nskemish/medmentum/application/fltr/png/ADDBTN.png

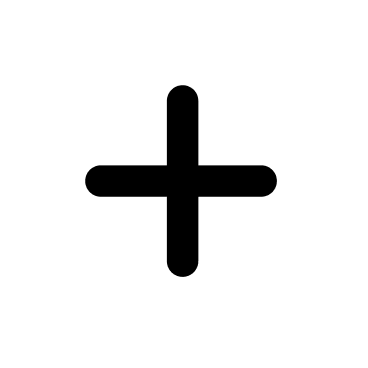
application/fltr/png/ADDBTN.png
