nskemish/medmentum/application/fltr/png/BATTERY.png

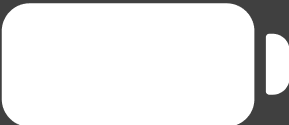
application/fltr/png/BATTERY.png
