nskemish/medmentum/application/fltr/png/DELBTN.png

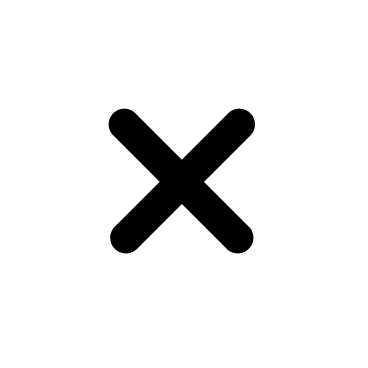
application/fltr/png/DELBTN.png
