nskemish/medmentum/application/fltr/png/DOZERI_IKONA.png

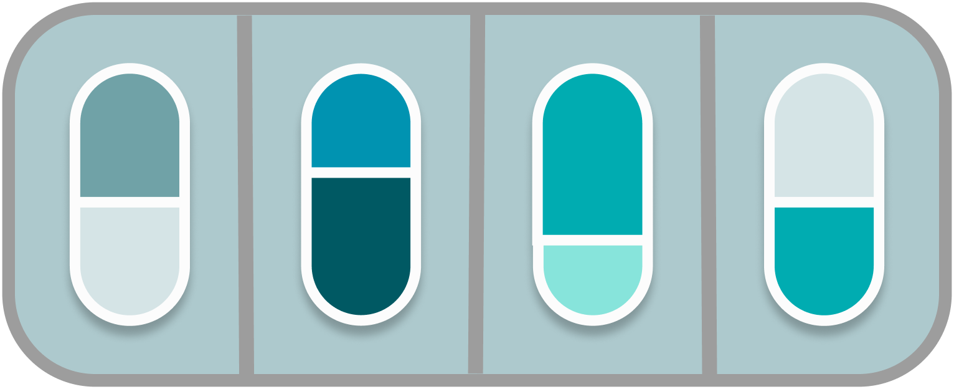
application/fltr/png/DOZERI_IKONA.png
