nskemish/medmentum/application/fltr/png/Ellipse 1.png

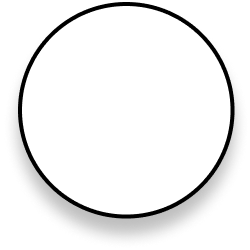
application/fltr/png/Ellipse 1.png
