nskemish/medmentum/application/fltr/png/Ellipse 2.png

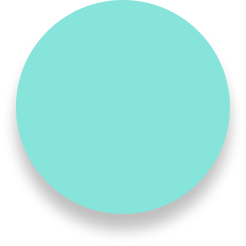
application/fltr/png/Ellipse 2.png
