nskemish/medmentum/application/fltr/png/OTKACENO.png

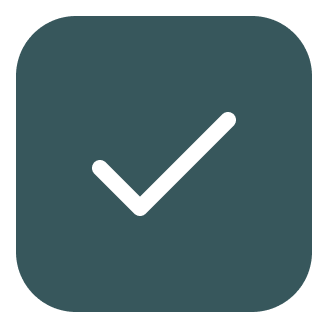
application/fltr/png/OTKACENO.png
