nskemish/medmentum/application/fltr/png/PILULA.png

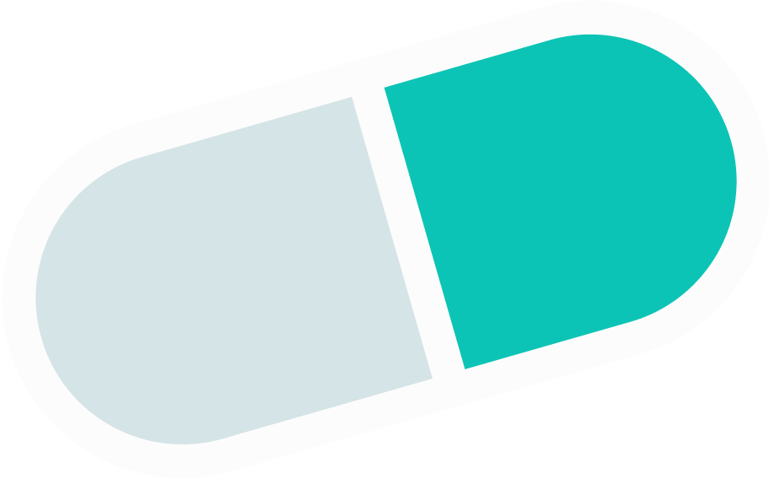
application/fltr/png/PILULA.png
