nskemish/medmentum/application/fltr/png/POVEZIVANJEDUGME.png

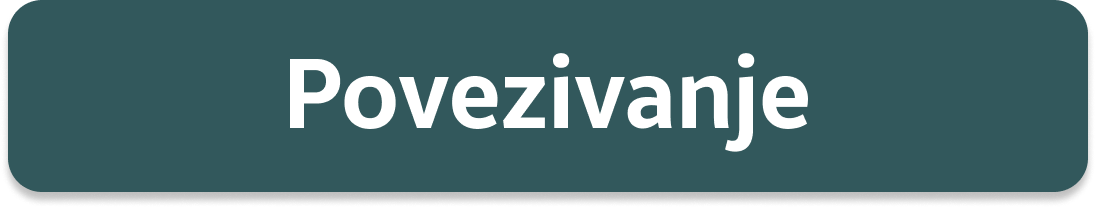
application/fltr/png/POVEZIVANJEDUGME.png
