nskemish/medmentum/device/hw/$d/slk/bulb-svgrepo-com.png

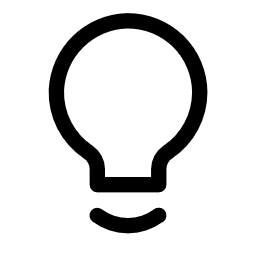
device/hw/$d/slk/bulb-svgrepo-com.png
