nskemish/medmentum/device/hw/$d/slk/MedMentum.png

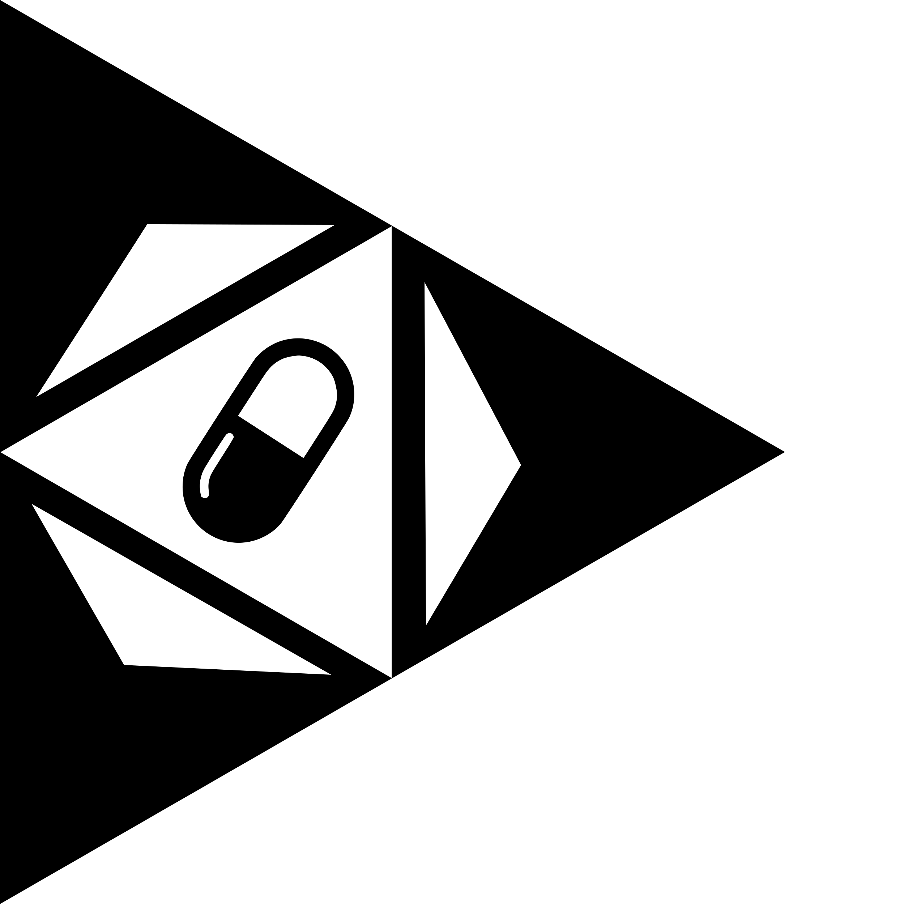
device/hw/$d/slk/MedMentum.png
