nskemish/medmentum/device/hw/$d/slk/NoviSad.png

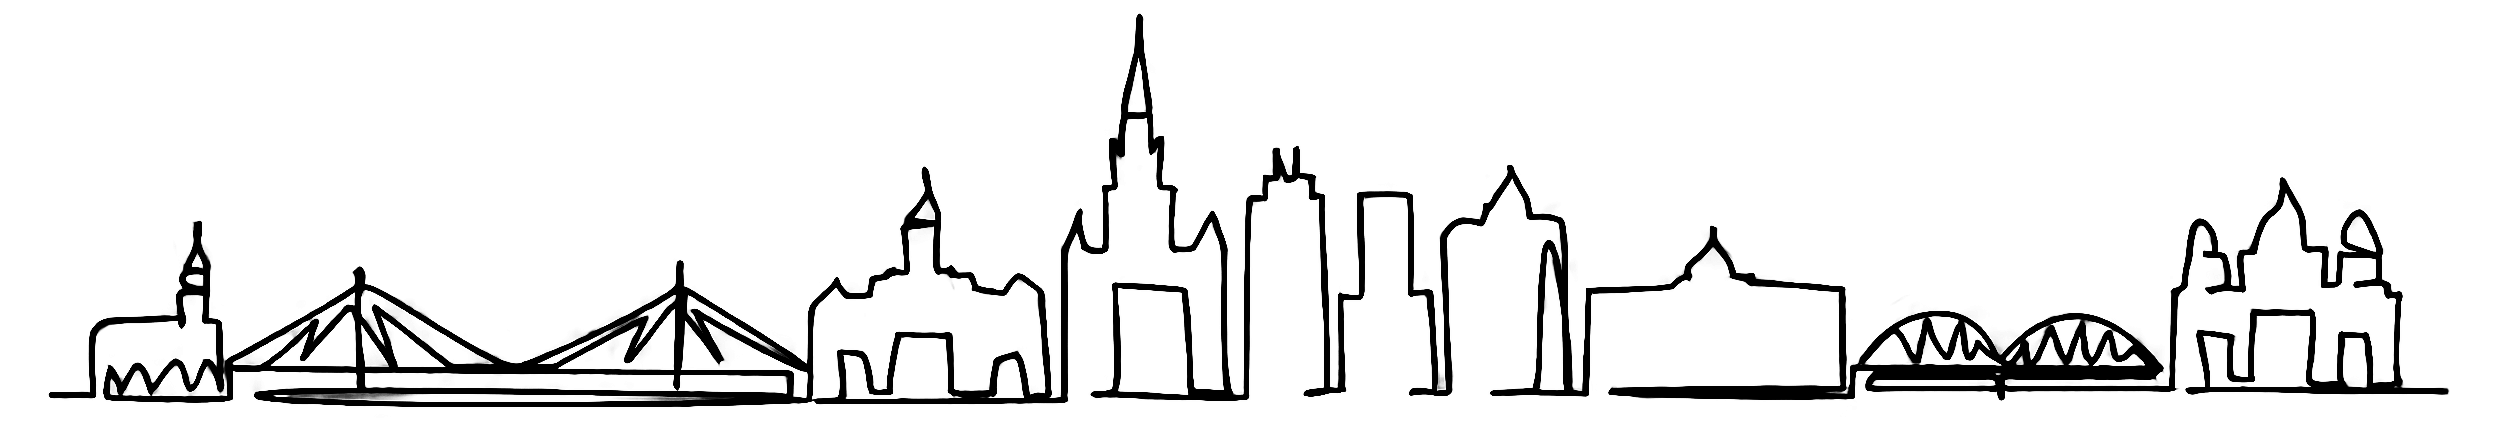
device/hw/$d/slk/NoviSad.png
