nskemish/medmentum/resources/visuals/png/medmentum/512x/partsx512/trianglex512.png

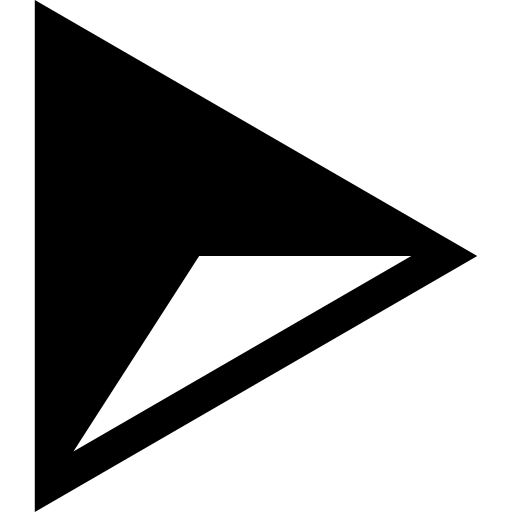
resources/visuals/png/medmentum/512x/partsx512/trianglex512.png
