nskemish/medmentum/resources/visuals/png/mm_long.png

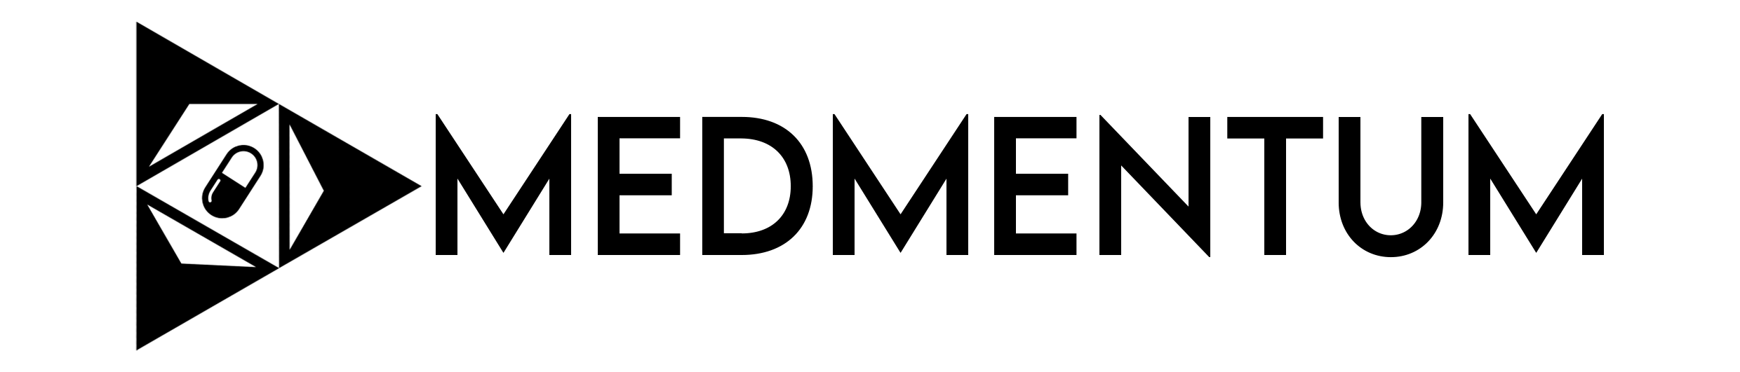
resources/visuals/png/mm_long.png
