nskemish/medmentum/resources/visuals/png/mm_short.png

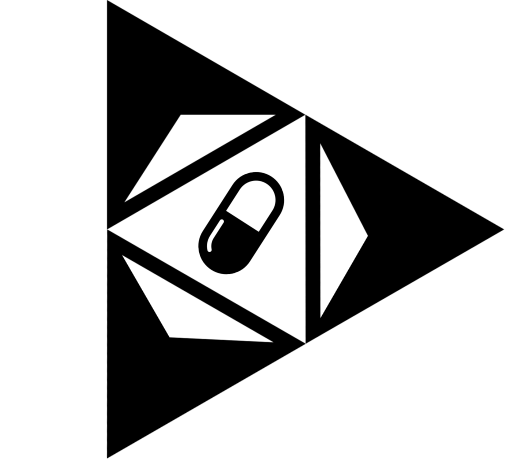
resources/visuals/png/mm_short.png
