nskemish/medmentum/resources/visuals/png/other/etš.png

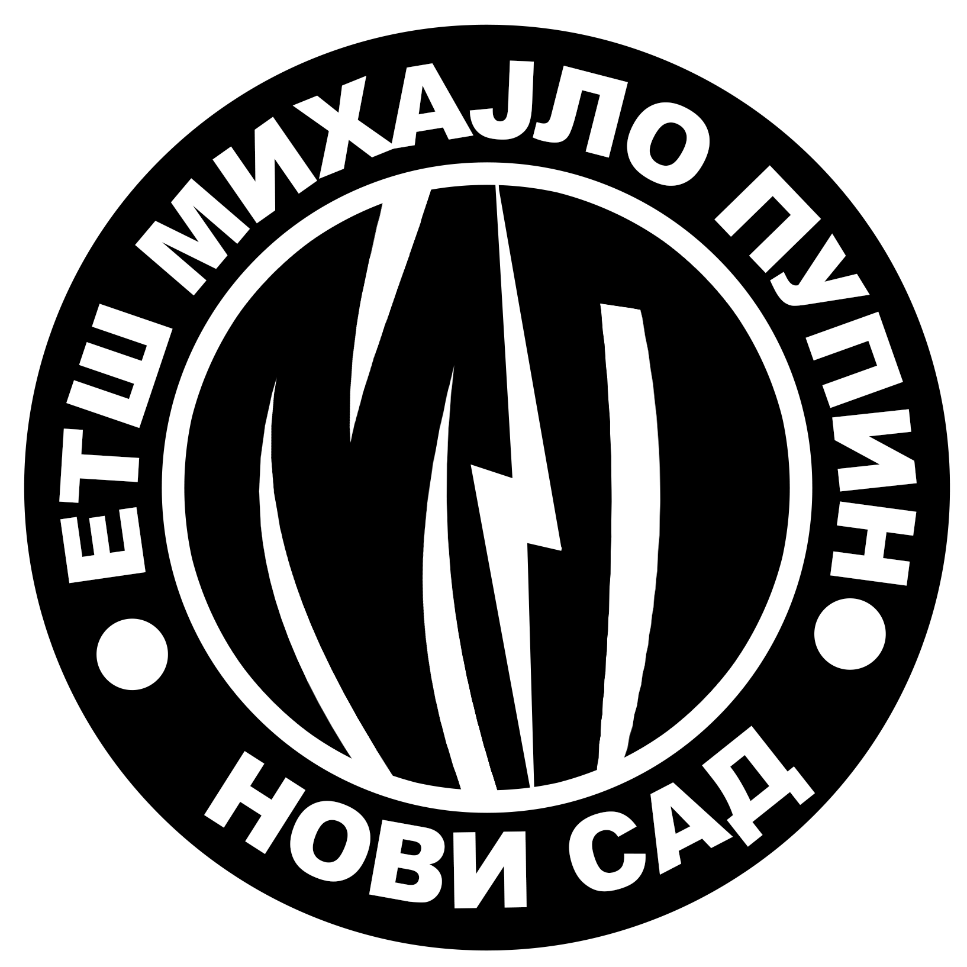
resources/visuals/png/other/etš.png
