nskemish/medmentum/resources/visuals/presentation/bg/bg1.png

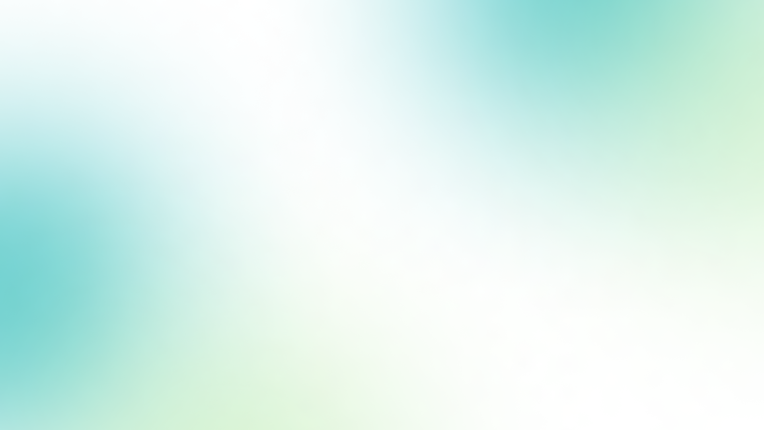
resources/visuals/presentation/bg/bg1.png
