nskemish/medmentum/resources/visuals/presentation/bg/bg2.png

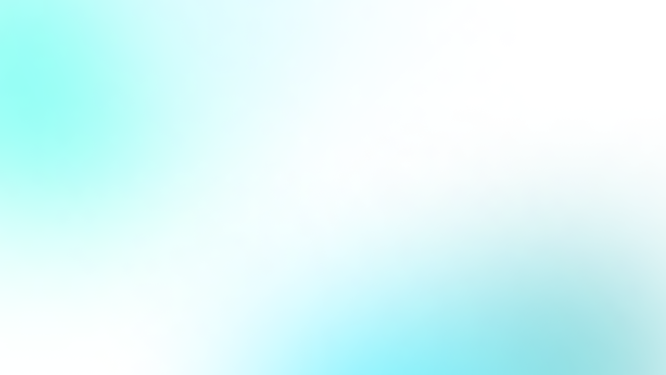
resources/visuals/presentation/bg/bg2.png
