nskemish/medmentum/resources/visuals/presentation/bg/bg3.png

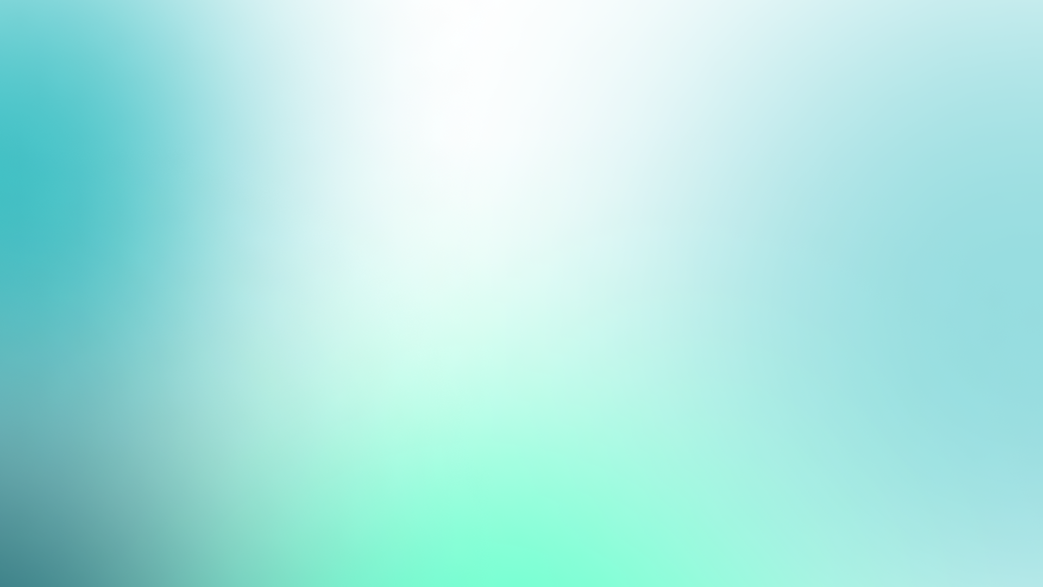
resources/visuals/presentation/bg/bg3.png
