nskemish/medmentum/resources/visuals/presentation/bg/bg4-1.png

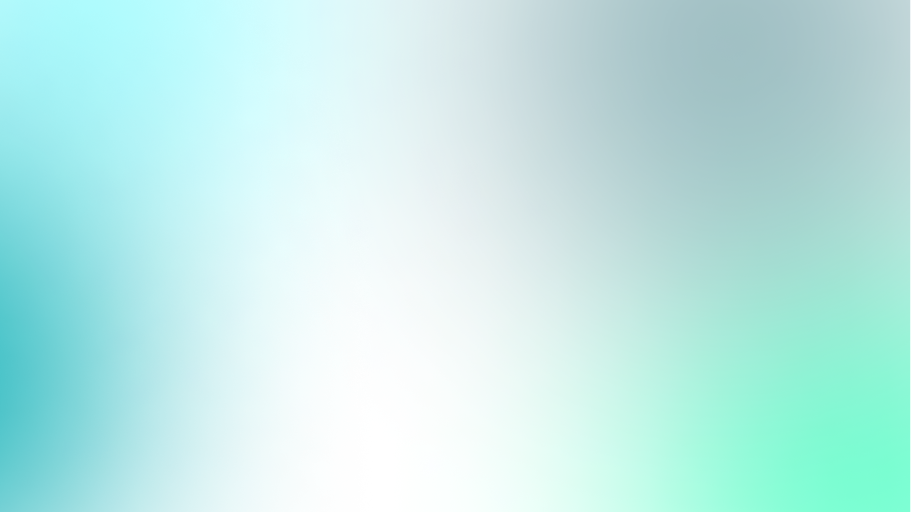
resources/visuals/presentation/bg/bg4-1.png
