nskemish/medmentum/resources/visuals/presentation/bg/bg5.png

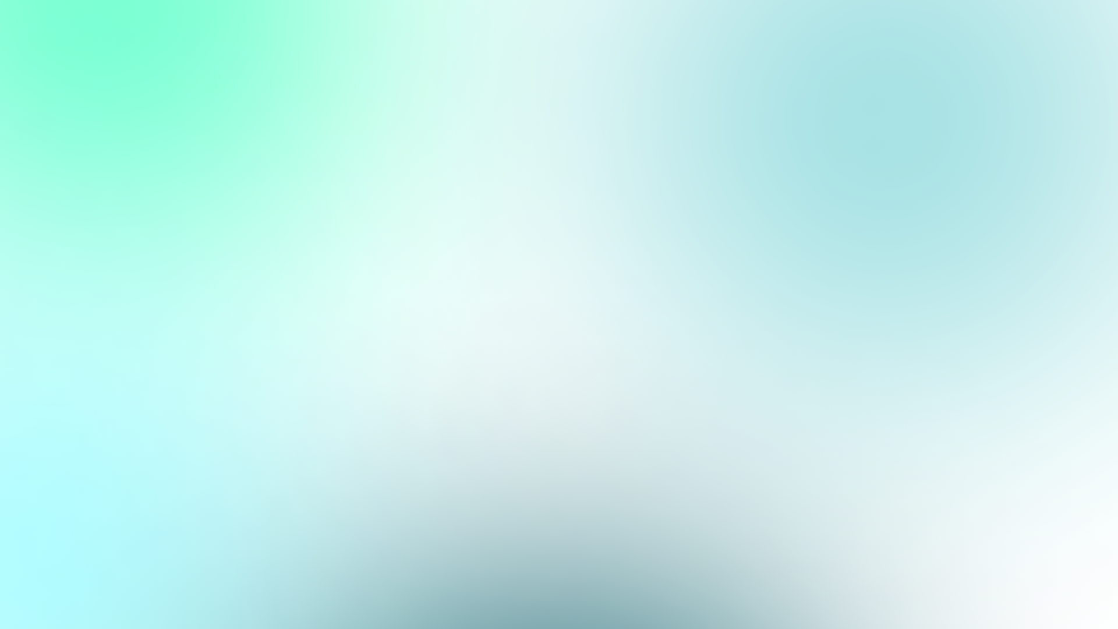
resources/visuals/presentation/bg/bg5.png
