nskemish/medmentum/resources/visuals/presentation/bg/bg6.png

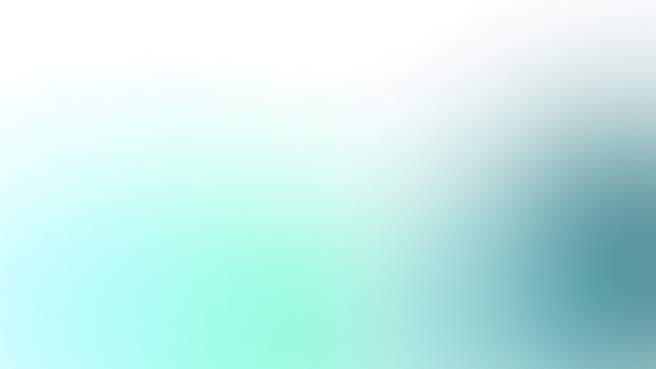
resources/visuals/presentation/bg/bg6.png
