nskemish/medmentum/webtools/site/assets/css/images/background.png

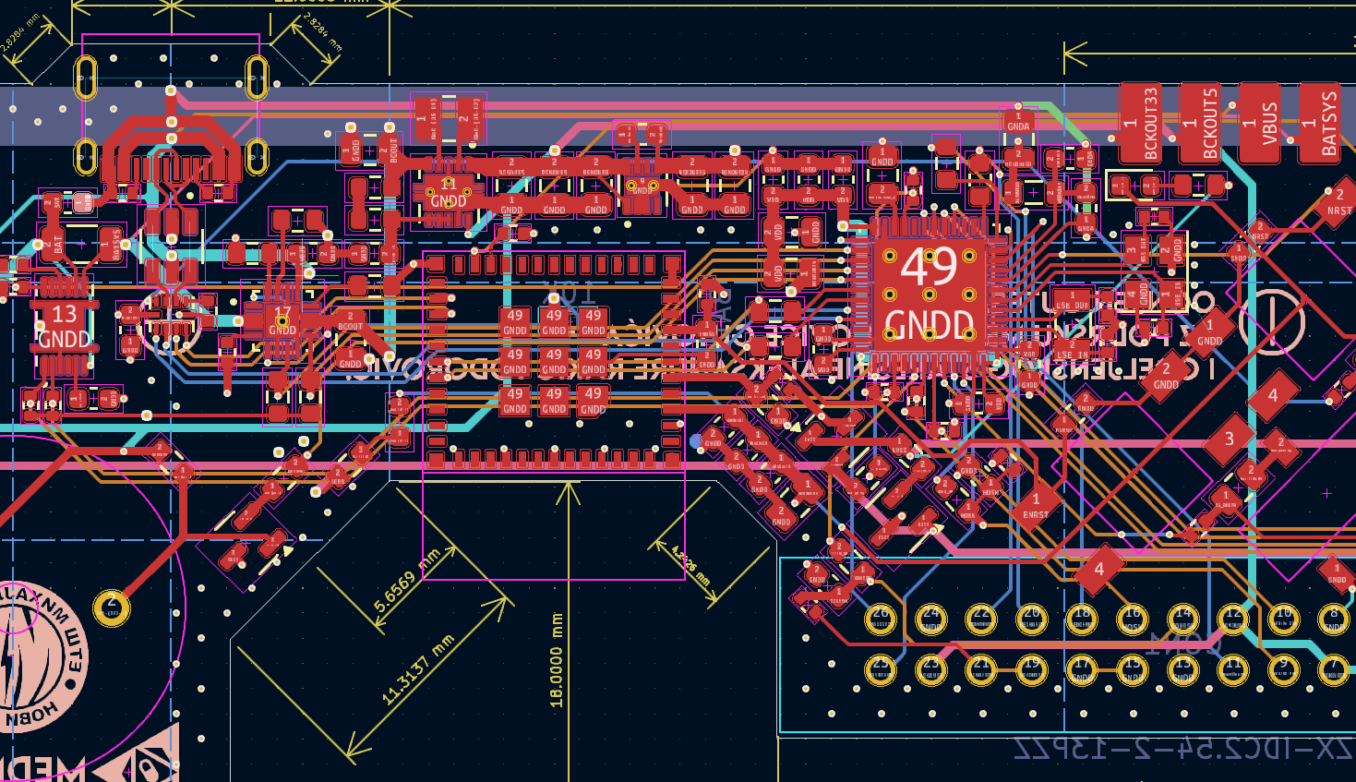
webtools/site/assets/css/images/background.png
